ZubairuGamidov/6V-DC-Charge-Pump-Converter/NE555_ChargePump_Simulation.asc

C1: polcap; 100µ; Rser=1
C2: polcap; 100µ; Rser=1
C3: polcap; 100µ; Rser=1
C4: Cap; 2.2n
C6: polcap; 100µ; Rser=1
C9: polcap; 2.2n
D1: schottky; 1N5819
D2: schottky; 1N5819
D3: schottky; 1N5819
D4: schottky; 1N5819
Int.Imp: Res; 50
Load: Res; 560
Out: polcap; 100µ; Rser=1
Q1: npn; BC238
Q2: pnp; BC308
R1: res; 2.2k
R2: Res; 3.3k
R3: Res; 470
RA: Res; 1.2k
RB: Res; 12k
Ripple: Cap; 0.47µ
U1: NE555
Vcc: Voltage; 6V
Named nets: 0, Vout, Vcc, .
.tran 0 500m 499m
.include BC308.txt
.include BC238.txt
